Jaroslav-Dvorak/PicoInk/3D/FCStd model/Display_holder.FCStd

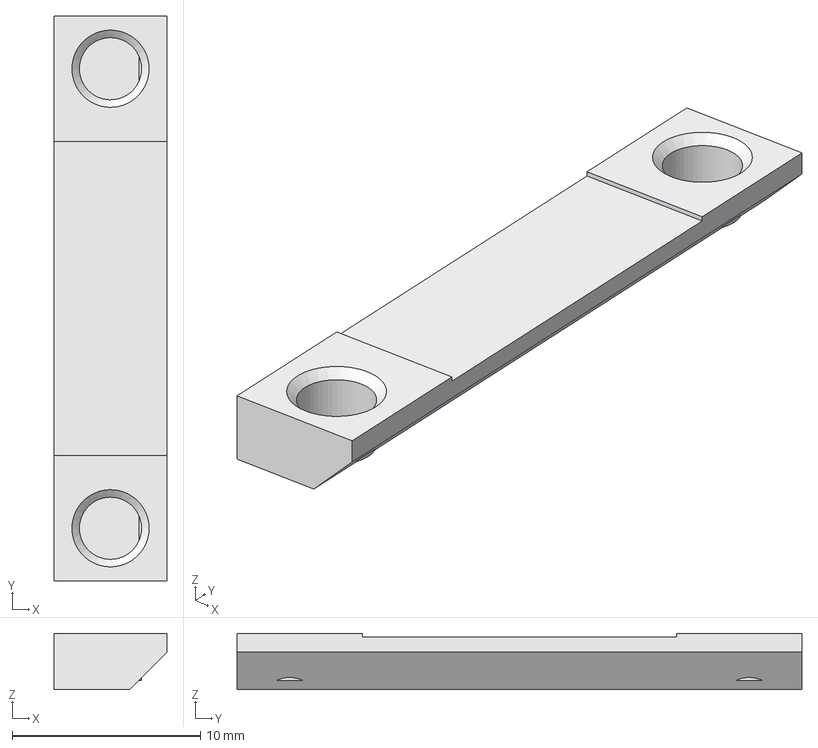
[picture p22: CAD file, 2024-09-10]
3D/FCStd model/Display_holder.FCStd
6.00 x 30.0 x 3.00 mm
