Jaroslav-Dvorak/PicoInk/3D/FCStd model/Light_guide.FCStd

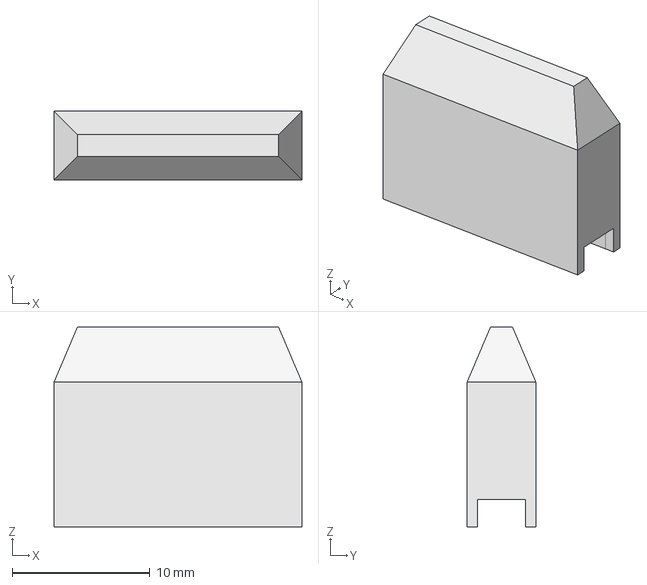
[picture p23: CAD file, 2024-09-10]
3D/FCStd model/Light_guide.FCStd
18.0 x 5.00 x 14.5 mm
