Jaroslav-Dvorak/PicoInk/3D/FCStd model/Modul_base.FCStd

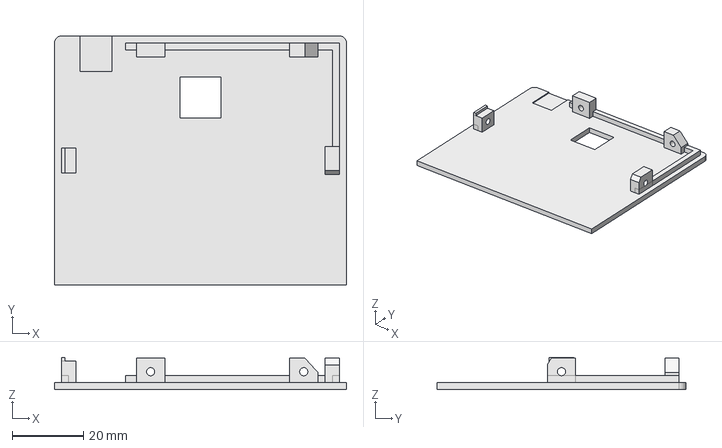
[picture p24: CAD file, 2024-08-21]
3D/FCStd model/Modul_base.FCStd
82.0 x 70.0 x 9.00 mm
