Jaroslav-Dvorak/PicoInk/Code/modes/mode_regular.py

import lib.display.screens as screens
from nonvolatile import Settings, save_value, get_last_values, num_to_byte, byte_to_num


def load_show_save(full_refresh, bat_soc, sensor):
    minimum = sensor.displ_min
    maximum = sensor.displ_max
    try:
        sensor_ok = sensor.get_values()
    except Exception as e:
        print(e)
        sensor_ok = False
        return sensor_ok

    value = list(sensor.last_values.items())[0][1]

    filesize, byte_values = get_last_values(249, "temperatures.dat")

    values = [byte_to_num(val, minimum, maximum) for val in byte_values]
    values.append(value)

    if full_refresh or filesize % 100 == 0:
        full_refresh = True

    if Settings["widget"] == 0:
        screens.show_chart(values, minimum, maximum, bat_soc, full_refresh)
    elif Settings["widget"] == 1:
        screens.show_big_val(value, bat_soc, full_refresh)
    elif Settings["widget"] == 2:
        screens.show_gauge(value, minimum, maximum, bat_soc, full_refresh)

    one_byte_value = num_to_byte(value, minimum, maximum)
    save_value(one_byte_value, "temperatures.dat")

    return sensor_ok
